devjonathanday/JonBoy/v2_STL/PiStrap_Lower.stl

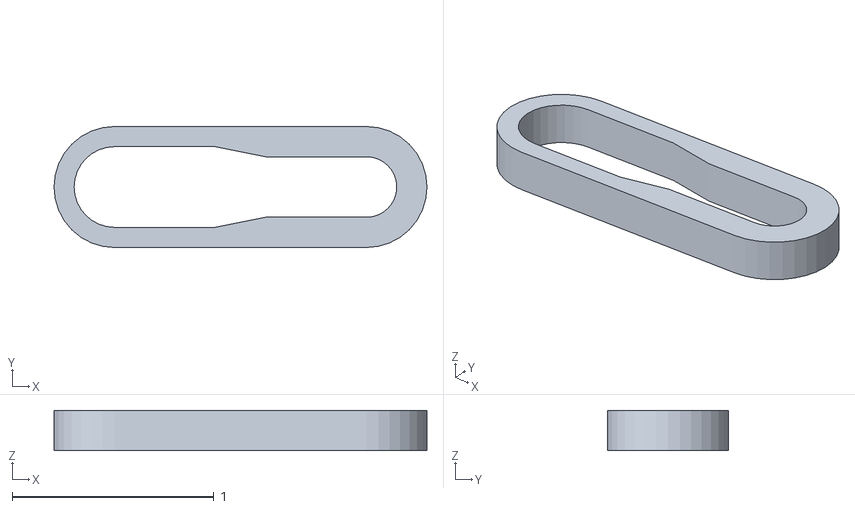
[picture p14: CAD file, 2022-04-17]
v2_STL/PiStrap_Lower.stl
1.85 x 0.6 x 0.2
