devjonathanday/JonBoy/v2_STL/Vent.stl

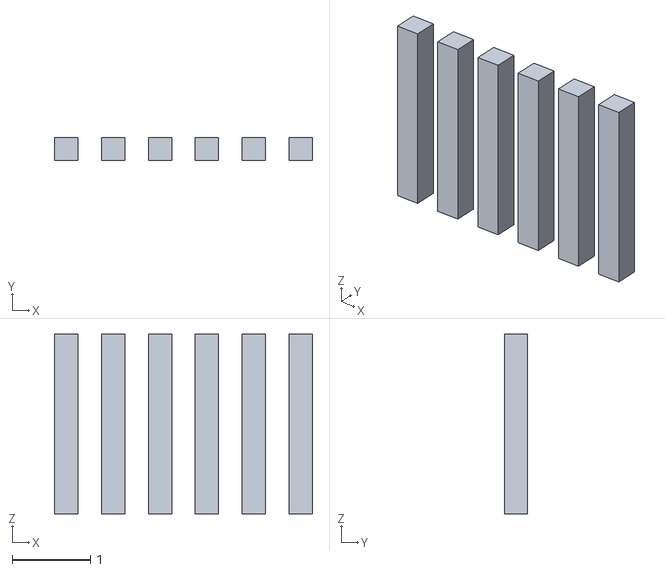
[picture p15: CAD file, 2022-04-17]
v2_STL/Vent.stl
3.30 x 0.3 x 2.30
