devjonathanday/JonBoy/v2_STL/DPadSurface.stl

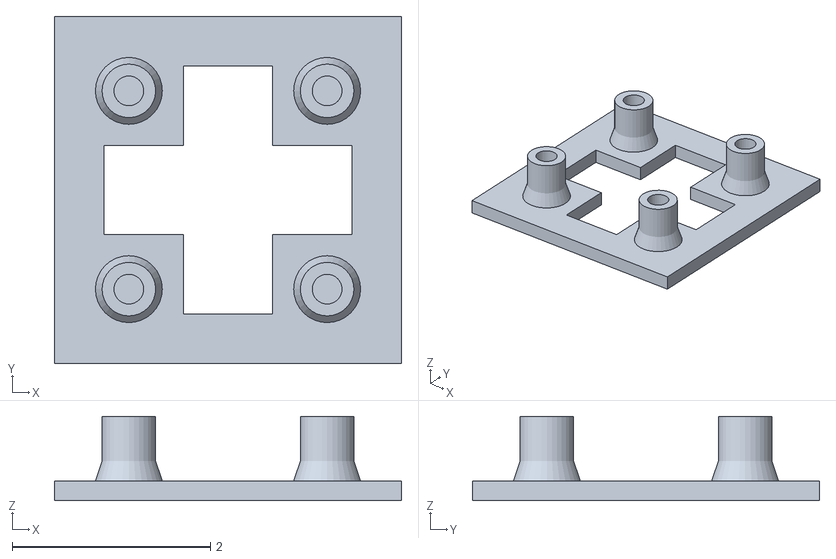
[picture p16: CAD file, 2022-04-17]
v2_STL/DPadSurface.stl
3.50 x 3.50 x 0.85
