devjonathanday/JonBoy/v2_STL/PowerButtonStrap.stl

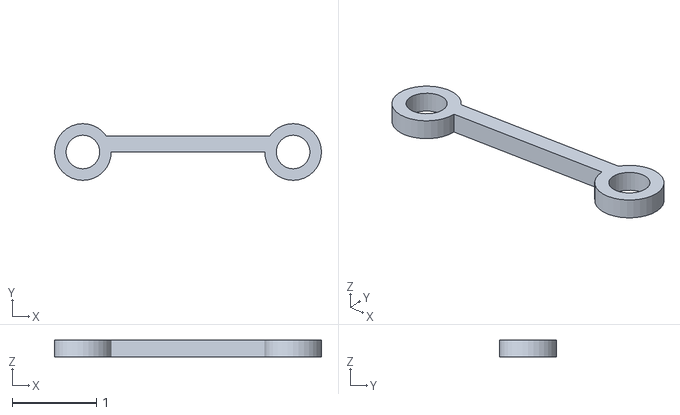
[picture p17: CAD file, 2022-04-17]
v2_STL/PowerButtonStrap.stl
3.17 x 0.675 x 0.2
