devjonathanday/JonBoy/v2_STL/Backplate_Center.stl

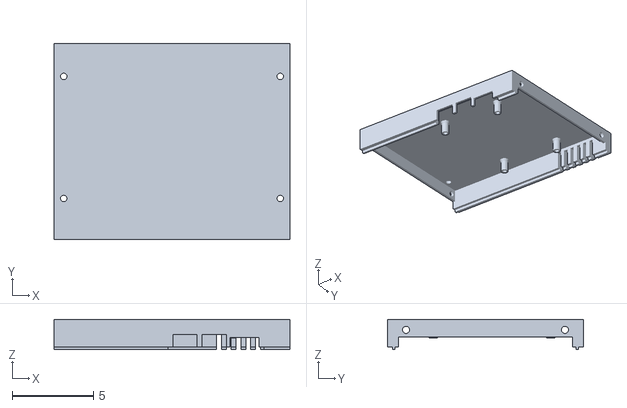
[picture p18: CAD file, 2022-04-17]
v2_STL/Backplate_Center.stl
14.6 x 12.1 x 1.88
