devjonathanday/JonBoy/v2_STL/BatteryBracketTest.stl

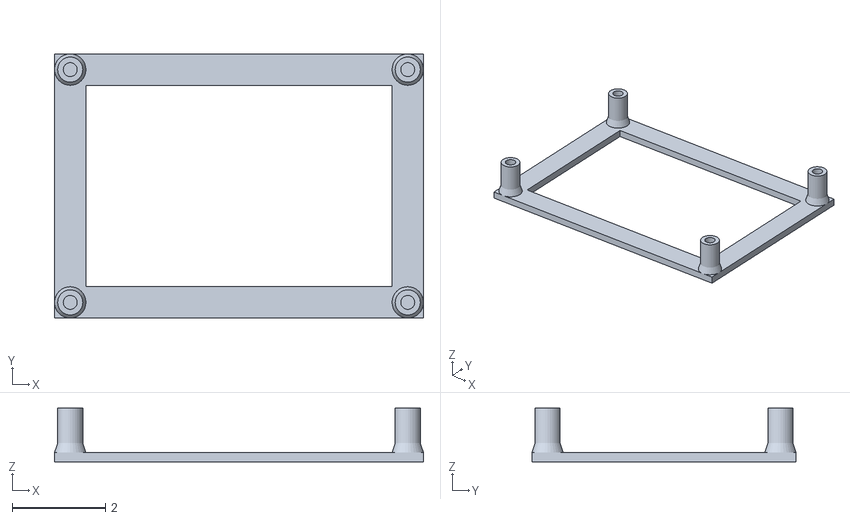
[picture p19: CAD file, 2022-04-17]
v2_STL/BatteryBracketTest.stl
7.93 x 5.68 x 1.15
