devjonathanday/JonBoy/v2_STL/PowerButton.stl

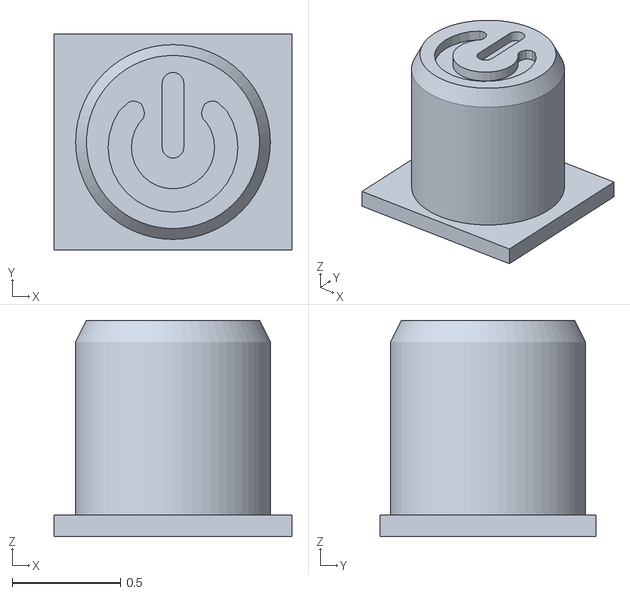
[picture p20: CAD file, 2022-04-17]
v2_STL/PowerButton.stl
1.10 x 1.00 x 1.00
