devjonathanday/JonBoy/v2_STL/4ButtonMount.stl

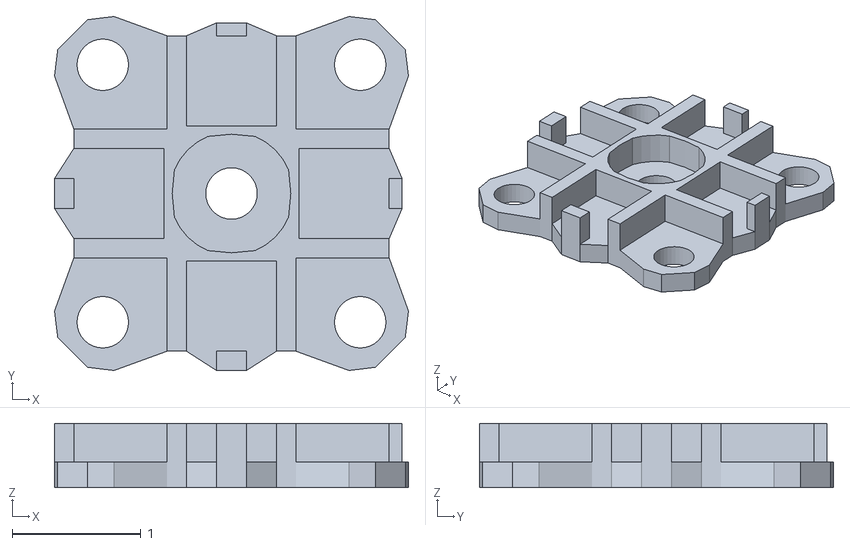
[picture p21: CAD file, 2022-04-17]
v2_STL/4ButtonMount.stl
2.75 x 2.75 x 0.5
