devjonathanday/JonBoy/v2_STL/PowerButtonTest.stl

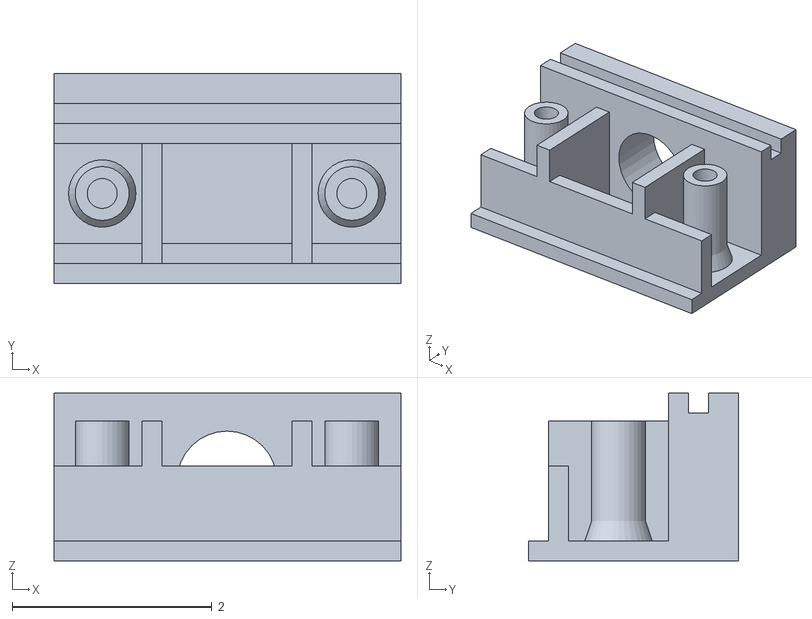
[picture p22: CAD file, 2022-04-13]
v2_STL/PowerButtonTest.stl
3.48 x 2.10 x 1.68
