devjonathanday/JonBoy/v2_STL/PowerButtonFrame.stl

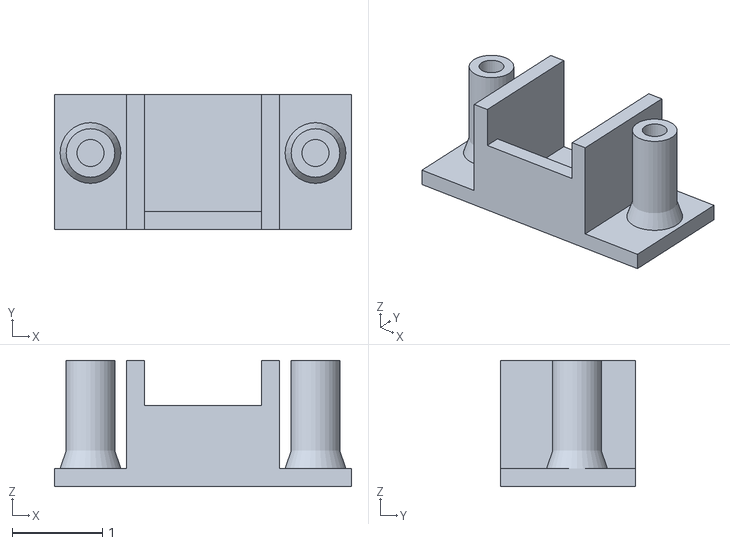
[picture p23: CAD file, 2022-04-13]
v2_STL/PowerButtonFrame.stl
3.30 x 1.50 x 1.40
