devjonathanday/JonBoy/v2_STL/ChargingPort.stl

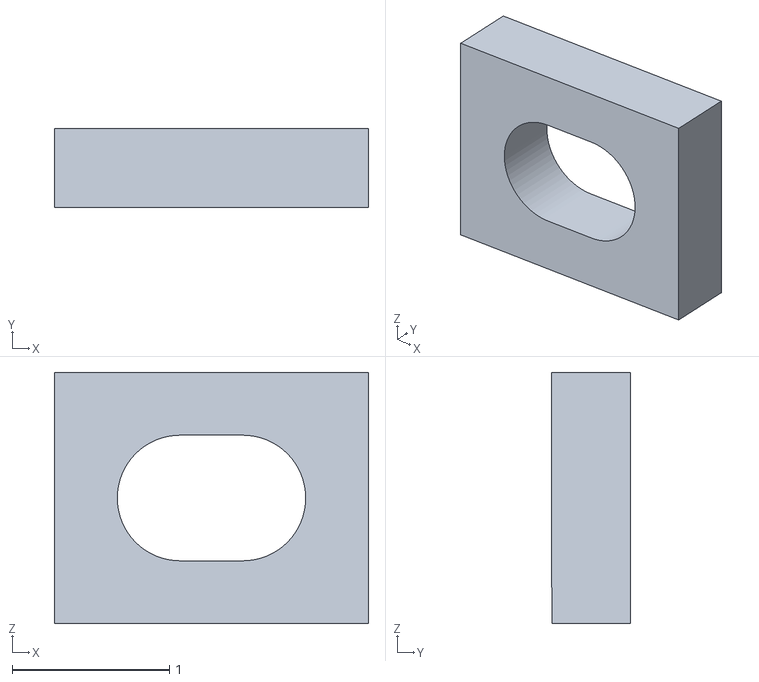
[picture p24: CAD file, 2022-04-11]
v2_STL/ChargingPort.stl
2.00 x 0.5 x 1.60
