devjonathanday/JonBoy/v2_STL/Shoulder_R.stl

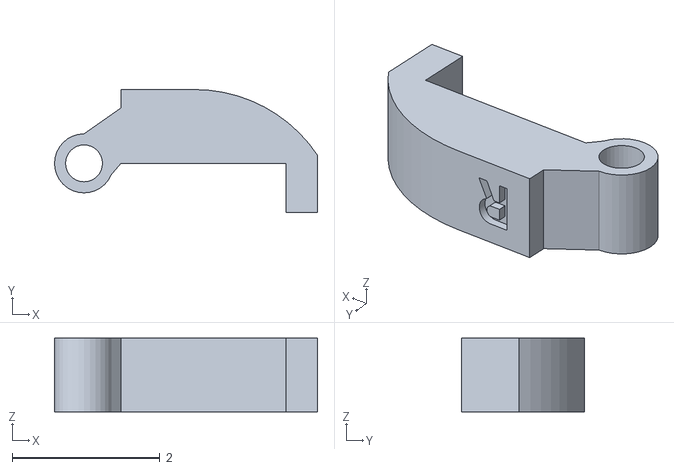
[picture p25: CAD file, 2022-04-10]
v2_STL/Shoulder_R.stl
3.56 x 1.66 x 1.00
