devjonathanday/JonBoy/v2_STL/Shoulder_R_Cutaway.stl

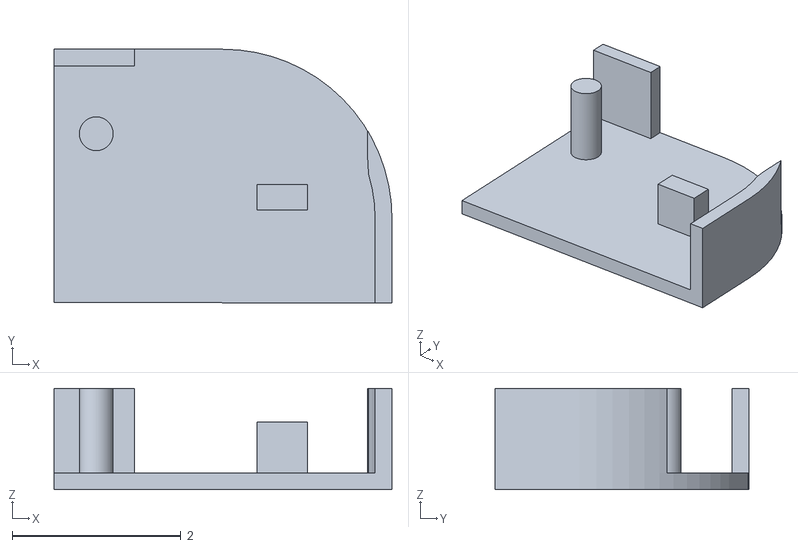
[picture p26: CAD file, 2022-04-09]
v2_STL/Shoulder_R_Cutaway.stl
4.00 x 3.00 x 1.20
